turhancan97/LLC-Resonant-Converter-and-Battery-Charge-Discharge-Regression-Model/Machine Learning Part/Random_Forest_skorlar.PNG

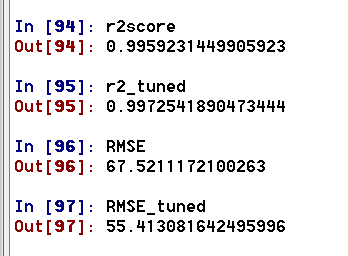
Machine Learning Part/Random_Forest_skorlar.PNG
