turhancan97/LLC-Resonant-Converter-and-Battery-Charge-Discharge-Regression-Model/Machine Learning Part/şarj-deşarj1.PNG

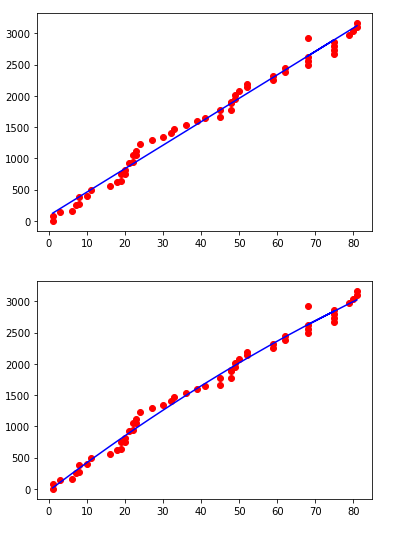
Machine Learning Part/şarj-deşarj1.PNG
