turhancan97/LLC-Resonant-Converter-and-Battery-Charge-Discharge-Regression-Model/Simulation/Simulation_Image.PNG

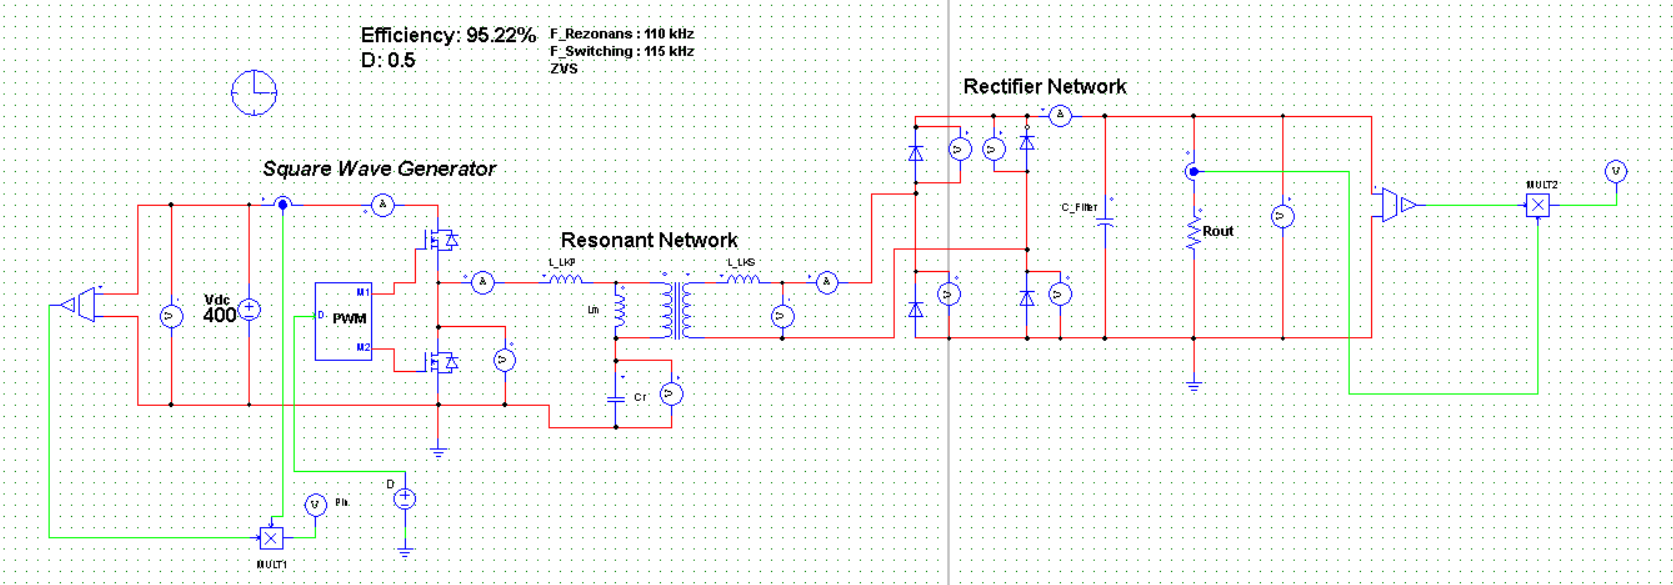
Simulation/Simulation_Image.PNG
